VersusBox/cad/ctrl_panel_bottom.FCStd

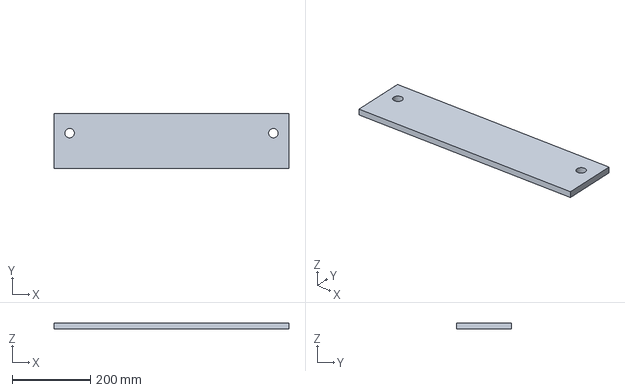
[picture p23: CAD file, 2025-08-10]
ctrl_panel_bottom.FCStd
600.0 x 140.0 x 15.0 mm
