VersusBox/cad/speaker_panel.FCStd

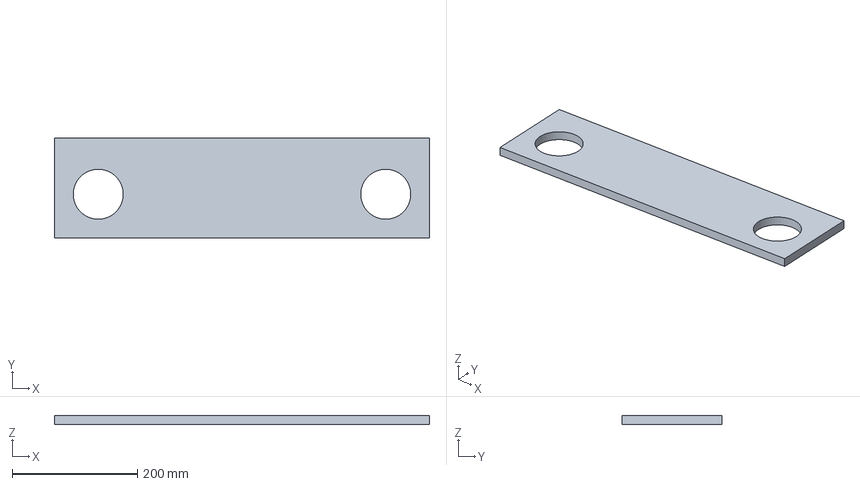
[picture p24: CAD file, 2025-08-10]
speaker_panel.FCStd
600.0 x 160.0 x 15.0 mm
