VersusBox/cad/control_panel.FCStd

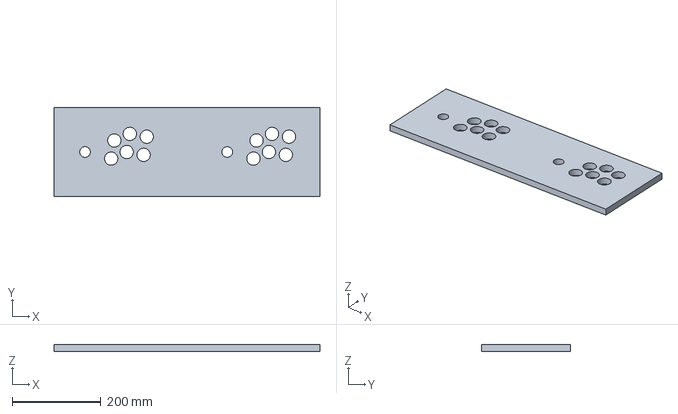
[picture p25: CAD file, 2025-08-10]
control_panel.FCStd
600.0 x 200.0 x 15.0 mm
