VersusBox/cad/glass.FCStd

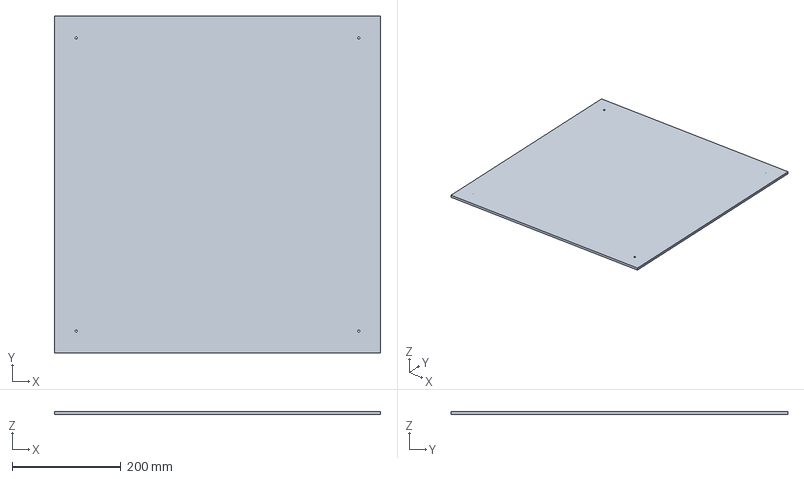
[picture p26: CAD file, 2025-08-10]
glass.FCStd
600.0 x 620.0 x 6.00 mm
