VersusBox/cad/back_bottom_door.FCStd

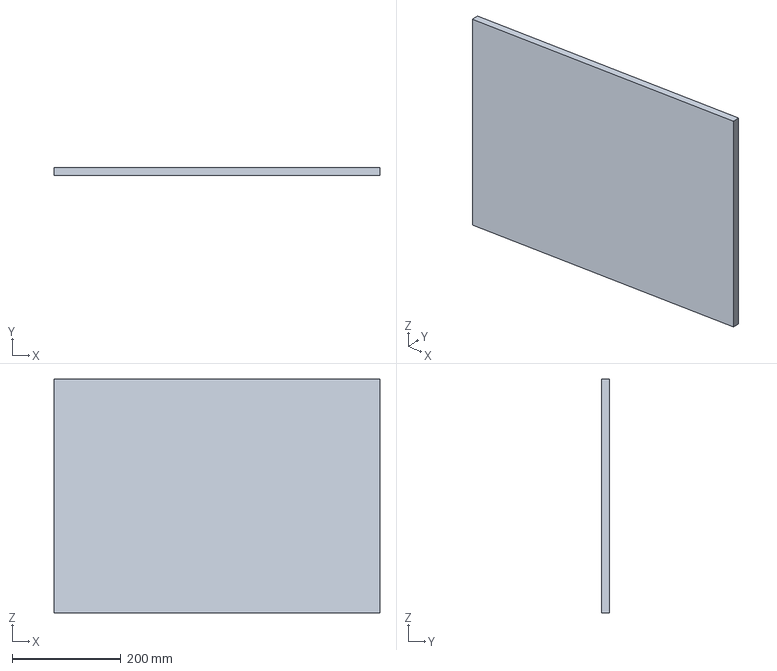
[picture p27: CAD file, 2025-08-10]
back_bottom_door.FCStd
600.0 x 15.0 x 430.0 mm
