VersusBox/cad/back_bottom.FCStd

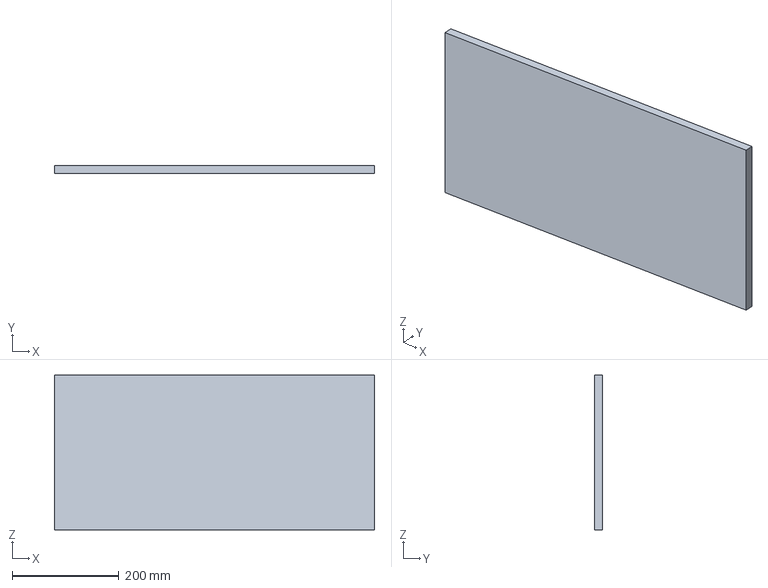
[picture p28: CAD file, 2025-08-10]
back_bottom.FCStd
600.0 x 15.0 x 290.0 mm
