VersusBox/cad/fan_plane.FCStd

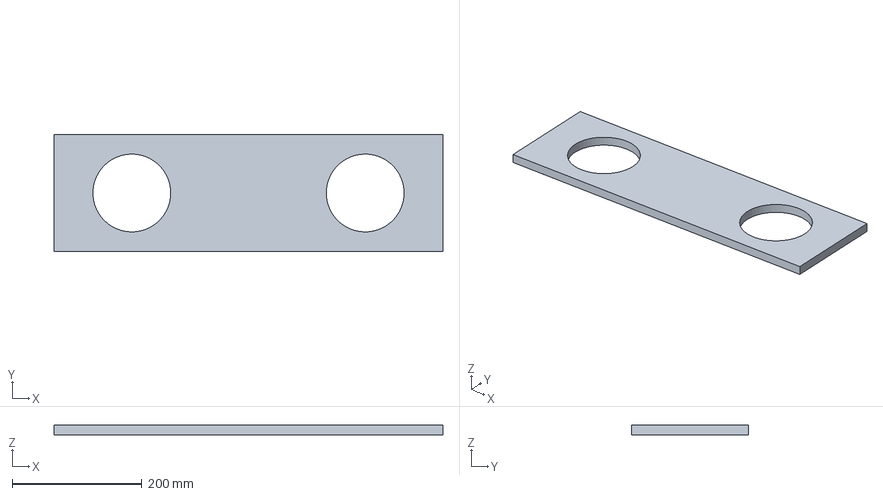
[picture p29: CAD file, 2025-08-10]
fan_plane.FCStd
600.0 x 180.0 x 15.0 mm
