VersusBox/cad/bottom.FCStd

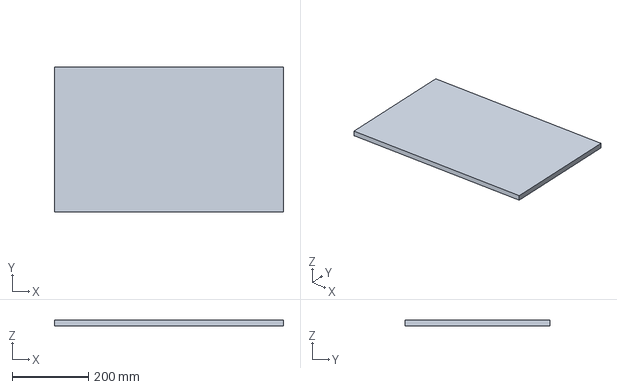
[picture p30: CAD file, 2025-08-10]
bottom.FCStd
600.0 x 380.0 x 15.0 mm
