VersusBox/cad/ctrl_panel_front.FCStd

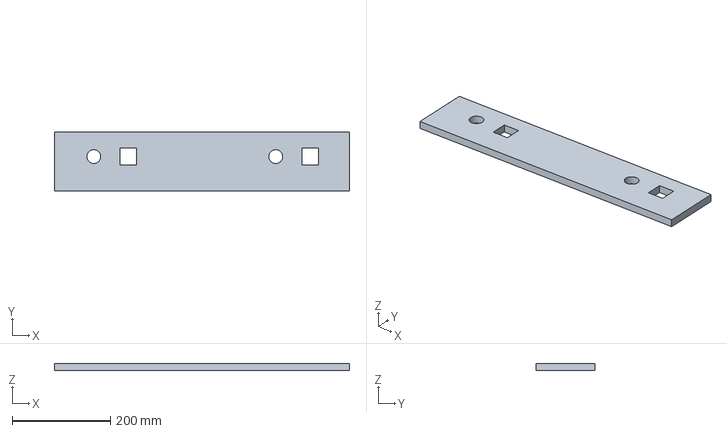
[picture p31: CAD file, 2025-08-10]
ctrl_panel_front.FCStd
600.0 x 120.0 x 15.0 mm
