VersusBox/cad/connector_panel.FCStd

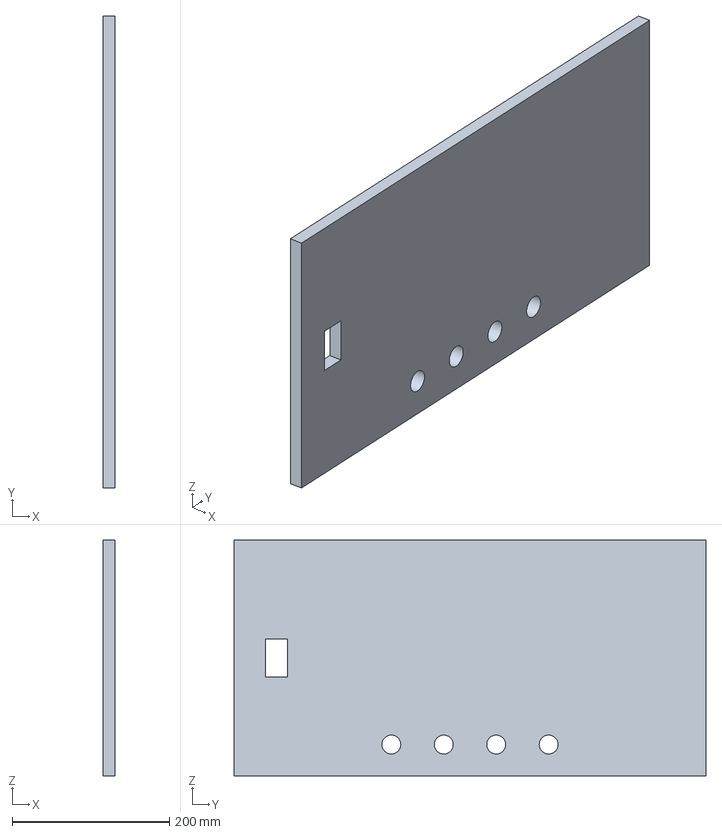
[picture p32: CAD file, 2025-08-10]
connector_panel.FCStd
15.0 x 600.0 x 300.0 mm
